w5xd/PacketThermometer/BatteryExtender.asc

C10: cap; 10µ; V=16 Irms=11 Rser=0.00378043 Lser=0 mfg="KEMET" pn="C0805C106K4PAC" type="X5R"
C11: cap; 10µ; V=16 Irms=11 Rser=0.00378043 Lser=0 mfg="KEMET" pn="C0805C106K4PAC" type="X5R"
D10: diode; Drb751v40t1g
D11: diode; Drb751v40t1g
D12: diode; Drb751v40t1g
nVportD3: voltage; PWL TIME_SCALE_FACTOR={PWM_HALF_PERIOD} VALUE_SCALE_FACTOR={VDD} REPEAT FOR {REPEAT_CYCLES} (0 1 .5 1 0.5001 0 {2 * PWM_CYCLES} 0 {.0004 + 2 * PWM_CYCLES} 1) ({REPEAT_INTERVAL_PERIOD} 1) ENDREPEAT; Rser=10 Cpar=1E-5
Q10: DMP3165L
Q11: DMN67D8L
Q12: DMP1045U
Q13: DMN67D8L
R1: res; 1e6
R2: res; 1e6
R9: res; 3.3e6
R10: res; 330
R11: res; 3.3e6
R12: res; 10000
R13: res; 1e6
U3: DMP2305U
V2: voltage; {VDD}; Rser=1
Vdd: voltage; PWL(0 0 .0001 {VDD}); Rser=1 Cpar=1e-5
VportD4: voltage; PWL TIME_SCALE_FACTOR={PWM_HALF_PERIOD} VALUE_SCALE_FACTOR={VDD} REPEAT FOR {REPEAT_CYCLES} REPEAT FOR {PWM_CYCLES} (0 0 {1-.0001} 0 1 1 {2 * 1-.0001} 1 2 0) ENDREPEAT ({REPEAT_INTERVAL_PERIOD} 0) ENDREPEAT; Rser=1 cPar=1e-5
Named nets: 0, VCharge, PortD3, VC11, HalfVdd
.tran 0 160 98 .0005
Battery Extender Circuit
Port D3 on Arduino is simulated by this nVPortD3+U3. Neither is on PCB.
Software holds port D3 at +Vdd during V1's PWM, then switches to INPUT
Port D4 runs 2msec PWM period for {PWM_CYCLES} cycles
P channel MOSFETS: Q12: 1V threshold or lower, 
    Q10: 2V threshold
N channel MOSFETS 2.5V threshold or lower
and ends (sleeps) holding 0V
.include "RB751V40T1G.LIB.txt"
.param VDD=3.3 PWM_CYCLES=3 PWM_HALF_PERIOD=.001 REPEAT_INTERVAL_PERIOD=1E5 REPEAT_CYCLES=2
