w5xd/PacketThermometer/BatteryExtenderLatch.asc

D12: diode; Drb751v40t1g
Q1: DMN67D8L
Q12: DMP1045U
Q13: DMN67D8L
R1: res; 1e6
R2: res; 1e6
R9: res; 3.3e6
R11: res; 3.3e6
R12: res; 10000
R13: res; 1e6
U3: DMP2305U
V1: voltage; PWL TIME_SCALE_FACTOR={PWM_HALF_PERIOD} VALUE_SCALE_FACTOR={VDD} REPEAT FOR 3 REPEAT FOR 3  (0 0 .9 0 1 1 1.9 1 2 0 4 0) ENDREPEAT (+0 0 +8 0) ENDREPEAT; Rser=10 Cpar=1E-7
V3: voltage; PWL(0 0 .0001 {VDD}); Rser=1 Cpar=1e-5
V4: voltage; PWL TIME_SCALE_FACTOR={PWM_HALF_PERIOD} VALUE_SCALE_FACTOR={VDD} (2 1) REPEAT FOR 3 REPEAT FOR 3  (0 1 .9 1 1 0 1.9 0 2 1 4 1) ENDREPEAT  (+0 1 +8 1) ENDREPEAT; Rser=10 Cpar=1E-7
Named nets: 0, PortD3, Vc11, HalfVdd
.tran 0 .1 0 .0005
Battery Extender Circuit
Port D3 on Arduino is simulated by this V4+U3. Neither is on PCB.
Software holds port D3 at +Vdd during V1's PWM, then switches to INPUT
P channel MOSFETS: Q12: 1V threshold or lower, 
    Q10: 2V threshold
N channel MOSFETS 2.5V threshold or lower
.include "RB751V40T1G.LIB.txt"
.param VDD=3.3 PWM_CYCLES=8 PWM_HALF_PERIOD=.001
Vdd
