w5xd/PacketThermometer/DeviceCurves.asc

D1: diode; Drb751v40t1g
R1: res; 1e4
R2: res; 1e4
U1: DMP1045U
V1: voltage; PWL(0 0 3.3 -3.3)
V2: voltage; -3.3
Named nets: 0
.include "RB751V40T1G.LIB.txt"
.tran 0 3.3 0
